kristofferkoch/oparroy/src/oparroy/dsl/ir.py

"""Core IR for the oparroy design-capture DSL (DESIGN.md §7).

The IR is a plain data structure — parts, pins, nets, one circuit —
built through the capture API (``Circuit.part`` / ``Circuit.net`` /
``Circuit.connect``: plain function calls in the HDL-instantiation
flavor, references are explicit instance names), validated by
``oparroy.dsl.check``, and consumed by the emitters. Structural
invariants (unique reference names, a pin on at most one net) raise at
construction; everything electrical is the validation pass's job.

Hierarchy is capture-time structure (§7): a circuit instantiates
subcircuits (``Circuit.instance``) with declared port interfaces
(``Circuit.port``), and ``Circuit.flatten`` is the pass that reduces
the hierarchy to the flat IR checks and emitters consume — instance
names prefix part references and internal nets, so identities stay
stable across source edits and findings report hierarchical paths.

Interfaces scale past scalar ports two ways (T7bb): port arrays
(``Circuit.port_array``) are width-fixed vectors bound element-wise,
and bundles (``Circuit.bundle``) group existing nets under member
names — the connector pinout as one connectable unit — bound
member-wise. Both expand to scalar port bindings at instantiation, so
flattening, checks, and emitters see plain nets only.

Multi-unit packages mirror KiCad's unit model (T7bc): ``Symbol``
preserves the unit structure, and a placed part instantiates a unit
subset — unplaced units materialize no pins, and a physical pin
shared by placed units is one ``Pin``, so KiCad ERC's shared-pin
one-net rule is structural in the IR. Component sockets
(``Circuit.socket``) let a subcircuit declare it needs a *part*, not
just nets: the instantiating parent directs the packing — a unit of a
parent-placed multi-unit package, or the socket protocol's standalone
default part — and the subcircuit stays package-agnostic.
"""

from __future__ import annotations

import re
from collections.abc import Iterable, Iterator, Mapping, Sequence
from dataclasses import dataclass
from enum import StrEnum
from typing import TYPE_CHECKING, ClassVar, Protocol, overload

if TYPE_CHECKING:
    from collections.abc import Callable

    from oparroy.dsl.parts import MultiUnitPart, TypedPart

type NetBinding = Net | str | Sequence[Net | str] | Mapping[str, Net | str]
type Connection = NetBinding | UnitHandle | type[TypedPart]

_NAT_SPLIT = re.compile(r"(\d+)")


def natural_key(text: str) -> tuple[tuple[str | int, ...], str]:
    """Sort key ordering embedded numbers numerically ("R2" < "R10").

    Keys equal after lowercasing and digit-splitting ("R1" vs "r1")
    fall back to the original string, so ordering never depends on
    insertion order.

    >>> natural_key("R10") > natural_key("R9")
    True
    """
    chunks = tuple(
        int(chunk) if chunk.isascii() and chunk.isdigit() else chunk
        for chunk in _NAT_SPLIT.split(text.lower())
    )
    return (chunks, text)


class PinType(StrEnum):
    """KiCad electrical pin types, valued as spelled in .kicad_sym files."""

    INPUT = "input"
    OUTPUT = "output"
    BIDIRECTIONAL = "bidirectional"
    TRI_STATE = "tri_state"
    PASSIVE = "passive"
    FREE = "free"
    UNSPECIFIED = "unspecified"
    POWER_IN = "power_in"
    POWER_OUT = "power_out"
    OPEN_COLLECTOR = "open_collector"
    OPEN_EMITTER = "open_emitter"
    NO_CONNECT = "no_connect"


class DefinitionError(Exception):
    """A structural IR invariant was violated during capture."""


def _reject_separator(kind: str, name: str) -> None:
    """Reject '/', the hierarchy path separator, in a captured name.

    Instance names, part references, and net names all become path
    elements under flattening (``WD1/Rs``, ``WD1/x``), so none may
    carry the separator — a '/' smuggled in at capture would collide
    with, or masquerade as, a flattened path.
    """
    if "/" in name:
        msg = f"{kind} {name!r} must not contain '/', the hierarchy path separator"
        raise DefinitionError(msg)


class UnknownSymbolError(DefinitionError):
    """A part referenced a symbol the symbol table does not know."""


_SOCKET_LIB = "socket"


def _pin_numbers(numbers: str | tuple[str, ...]) -> tuple[str, ...]:
    """Normalize a pin_map value to a tuple of pin numbers."""
    return (numbers,) if isinstance(numbers, str) else numbers


def _validate_socket_spec(spec: type[SocketSpec]) -> None:
    """Reject a malformed socket protocol at declaration."""
    # Lazy import: parts.py imports this module at runtime.
    from oparroy.dsl.parts import MultiUnitPart as _MultiUnitPart  # noqa: PLC0415
    from oparroy.dsl.parts import TypedPart as _TypedPart  # noqa: PLC0415

    if not (isinstance(spec, type) and issubclass(spec, SocketSpec)):
        msg = f"socket() needs a SocketSpec subclass, got {spec!r}"
        raise DefinitionError(msg)
    pins = getattr(spec, "pins", None)
    if (
        not isinstance(pins, tuple)
        or not pins
        or any(not isinstance(pin, str) or not pin for pin in pins)
        or len(set(pins)) != len(pins)
    ):
        msg = f"{spec.__name__}.pins must be a non-empty tuple of unique names"
        raise DefinitionError(msg)
    default = getattr(spec, "default", None)
    if not (isinstance(default, type) and issubclass(default, _TypedPart)):
        msg = f"{spec.__name__}.default must be a typed part class, got {default!r}"
        raise DefinitionError(msg)
    if issubclass(default, _MultiUnitPart):
        msg = (
            f"{spec.__name__}.default must be a standalone part, "
            f"not the multi-unit package {default.__name__}"
        )
        raise DefinitionError(msg)
    if set(default.pin_map) != set(pins):
        msg = (
            f"{spec.__name__}.default ({default.__name__}) has pins "
            f"{sorted(default.pin_map)}, not the protocol pins {sorted(pins)}"
        )
        raise DefinitionError(msg)


def _bind_part_class(
    name: str,
    ref: str,
    spec: type[SocketSpec],
    part_class: type[TypedPart],
) -> StandaloneSocket:
    """Validate a parent-directed standalone part class for a socket."""
    # Lazy import: parts.py imports this module at runtime.
    from oparroy.dsl.parts import MultiUnitPart as _MultiUnitPart  # noqa: PLC0415

    if issubclass(part_class, _MultiUnitPart):
        msg = (
            f"instance {name!r}: socket {ref!r} takes one unit of "
            f"{part_class.__name__} (u1.unit(3)), not the whole package"
        )
        raise DefinitionError(msg)
    if set(part_class.pin_map) != set(spec.pins):
        msg = (
            f"instance {name!r}: {part_class.__name__} does not satisfy "
            f"socket {ref!r}: pin names {sorted(part_class.pin_map)} != "
            f"protocol {sorted(spec.pins)}"
        )
        raise DefinitionError(msg)
    return StandaloneSocket(part_class=part_class)


@dataclass(frozen=True)
class Interval:
    """A closed interval [low, high] — one limit range.

    Containment is inclusive on both ends, so equal boundaries cover:

    >>> Interval(0, 3.6).contains(Interval(0, 3.3))
    True
    >>> Interval(0, 3.6).contains(Interval(0, 3.6))
    True
    >>> Interval(0, 3.3).contains(Interval(-0.3, 3.3))
    False
    """

    low: float
    high: float

    def __post_init__(self) -> None:
        if not self.low <= self.high:
            msg = f"interval low {self.low} exceeds high {self.high}"
            raise DefinitionError(msg)

    def contains(self, other: Interval) -> bool:
        """Return True when this interval fully covers ``other``."""
        return self.low <= other.low and other.high <= self.high

    def __str__(self) -> str:
        return f"{self.low}..{self.high}"


@dataclass(frozen=True)
class Limits:
    """A port's electrical limit ranges: voltage, optionally current.

    On a ``source`` port the ranges are what the driver puts out; on a
    ``sink`` port what the input accepts. The validation pass checks
    interval containment at instance bindings — the sink's range must
    cover the connected source's — so tolerance stackup is checkable
    data. ``current`` is optional: a port declaring voltage only checks
    voltage only.
    """

    voltage: Interval
    current: Interval | None = None

    def __str__(self) -> str:
        text = f"{self.voltage} V"
        if self.current is not None:
            text += f", {self.current} A"
        return text


@dataclass(frozen=True)
class Waiver:
    """An explicit, path-addressed check waiver: auditable data.

    Waivers live in the capture next to the wiring they excuse
    (``board.waive("range-containment", "WD1/ka", reason=...)``) — never
    comment-style suppression. ``path`` is the hierarchical path the
    finding reports. A waiver that matches no finding warns as stale.
    """

    check: str
    path: str
    reason: str


@dataclass(frozen=True)
class Provenance:
    """Base-design origin of a transform-created part or net.

    Instrumentation transforms (:mod:`oparroy.dsl.transform`) tag every
    part and net they create: ``transform`` is the transform record's
    label (``"F1"``), ``base`` the capture name of the base net it
    derives from, relative to the tile the transform applied in. The
    reset-state equivalence proof consumes exactly these tags —
    no name-matching heuristics. Base-capture elements carry None.
    """

    transform: str
    base: str


@dataclass(frozen=True, order=True)
class TileNet:
    """A net local to one tile instance, addressed for a pass's tables.

    The instance path plus the tile-local capture name —
    ``TileNet(("T0",), "sense")`` — identifies the net unambiguously
    across the board (it flattens to ``T0/sense``). The key shape of
    the transform ``Handles`` (:mod:`oparroy.dsl.transform`) and of the
    equivalence proof's reset-level and base-net tables: a named type
    because a bare ``tuple[tuple[str, ...], str]`` transposes its two
    components without a murmur (code-std-python.md#2-composite-types).

    >>> TileNet(("T0",), "sense").name
    'sense'
    """

    path: tuple[str, ...]
    name: str


@dataclass(frozen=True)
class Residuals:
    """Electrical residual magnitudes of a part in its pass-through state.

    The reset-state equivalence proof's magnitude source
    (``docs/instrumentation-equivalence.md`` §4 Q3): a closed analog
    switch is 7 Ω, not 0 Ω — the proof
    enumerates these per placed part against the residual register
    (``docs/instrumented-ci.md`` §9). Values come from the
    parts DB (``PartRecord.residuals``) via the typed part class; a
    field left None is no data, never zero. Geometry residuals (tap
    stub capacitance) are not expressible here — they are layout
    properties, emitted as layout-checker obligations.

    >>> r = Residuals(on_resistance_ohm=7.0, on_capacitance_pf=17.3)
    >>> r.on_resistance_ohm
    7.0
    """

    on_resistance_ohm: float | None = None
    on_capacitance_pf: float | None = None
    off_capacitance_pf: float | None = None
    leakage_ua: float | None = None

    def __post_init__(self) -> None:
        for field_name in (
            "on_resistance_ohm",
            "on_capacitance_pf",
            "off_capacitance_pf",
            "leakage_ua",
        ):
            value = getattr(self, field_name)
            if value is not None and value < 0:
                msg = f"residual {field_name} must not be negative, got {value}"
                raise DefinitionError(msg)


@dataclass(frozen=True)
class SymbolPin:
    """One pin of a library symbol: number, display name, electrical type."""

    number: str
    name: str
    type: PinType


@dataclass(frozen=True)
class SymbolUnit:
    """One placeable unit of a multi-unit symbol (DESIGN.md §7).

    KiCad encodes units as ``<Name>_<unit>_<style>`` subsymbols; each
    unit's pins carry physical package pin numbers, and one physical
    pin may appear in several units (the BAT54ADW shared anodes).
    """

    number: int
    pins: tuple[SymbolPin, ...]


@dataclass(frozen=True)
class Symbol:
    """A resolved library symbol: the pin-level contract of a part kind.

    ``pins`` is the all-units placement view; the unit structure
    (DESIGN.md §7) is ``common_pins`` — unit 0, present in every
    placed unit; the whole pin set of a single-unit symbol — and
    ``units``, the placeable units in unit-number order.
    """

    lib: str
    name: str
    pins: tuple[SymbolPin, ...]
    footprint_filters: tuple[str, ...] = ()
    pin_conflicts: tuple[str, ...] = ()
    common_pins: tuple[SymbolPin, ...] = ()
    units: tuple[SymbolUnit, ...] = ()

    @property
    def ref(self) -> str:
        """The canonical ``Lib:Name`` reference."""
        return f"{self.lib}:{self.name}"

    @property
    def is_power(self) -> bool:
        """True for power-library symbols (``power:+3V3``).

        Power symbols are schematic-only net markers: no footprint,
        excluded from the board netlist.
        """
        return self.lib == "power"

    @property
    def is_socket(self) -> bool:
        """True for component-socket placeholders (``Circuit.socket``).

        A socket placeholder carries the protocol pins a subcircuit
        wires against; flattening replaces it with the standalone part
        or the parent-placed package unit the parent directed.
        """
        return self.lib == _SOCKET_LIB

    def pin(self, number: str) -> SymbolPin | None:
        """Look up a pin by number, or None if the symbol has no such pin."""
        return next((p for p in self.pins if p.number == number), None)

    def pins_for_units(self, units: Iterable[int] | None) -> tuple[SymbolPin, ...]:
        """Return the pins a placement materializes for a unit subset.

        None places every unit (the default) — the whole ``pins``
        view. A subset places the common pins plus the chosen units'
        pins; unplaced units materialize no pins, so the
        unconnected-pin check stays clean. A physical pin shared by
        several placed units appears once.
        """
        if units is None:
            return self.pins
        known = {unit.number for unit in self.units}
        unknown = sorted(set(units) - known)
        if unknown:
            msg = f"{self.ref} has no units {unknown} (units: {sorted(known)})"
            raise DefinitionError(msg)
        wanted = set(units)
        merged: dict[str, SymbolPin] = {pin.number: pin for pin in self.common_pins}
        for unit in self.units:
            if unit.number in wanted:
                for pin in unit.pins:
                    merged[pin.number] = pin
        return tuple(merged.values())


class SymbolTable(Protocol):
    """Source of library symbols — kicadlib for real use, stubs in tests."""

    def lookup(self, ref: str) -> Symbol:
        """Resolve ``Lib:Name`` to a Symbol, raising UnknownSymbolError."""
        ...


class SocketSpec:
    """A component socket protocol: the pin handles a subcircuit needs.

    Subclasses (``oparroy.dsl.parts``) fix ``pins`` — the protocol pin
    names — and ``default``, the standalone typed part flattening
    places when the instantiating parent does not pack the socket into
    one unit of a parent-placed multi-unit package. Packing is the
    parent's directed choice; the subcircuit stays package-agnostic
    (DESIGN.md §7, T7bc).
    """

    pins: ClassVar[tuple[str, ...]]
    default: ClassVar[type[TypedPart]]


class Pin:
    """One pin of one placed part; carries its net membership."""

    def __init__(self, part: Part, symbol_pin: SymbolPin) -> None:
        self._part = part
        self._symbol_pin = symbol_pin
        self._net: Net | None = None

    @property
    def part(self) -> Part:
        """The part this pin belongs to."""
        return self._part

    @property
    def net(self) -> Net | None:
        """The net this pin sits on, or None; set only by circuit wiring."""
        return self._net

    @property
    def number(self) -> str:
        """The pin number as declared by the symbol ("1", "A3", ...)."""
        return self._symbol_pin.number

    @property
    def name(self) -> str:
        """The pin name as declared by the symbol ("" when unnamed)."""
        return self._symbol_pin.name

    @property
    def type(self) -> PinType:
        """The electrical type declared by the symbol."""
        return self._symbol_pin.type

    def __repr__(self) -> str:
        return f"<Pin {self._part.ref}.{self.number}>"


@dataclass(frozen=True)
class Placement:
    """How a placed part sits: hierarchy path and multi-unit selection.

    ``path`` is the instance path flattening stamps on the flat copy —
    the hierarchy metadata (sheetpath) the KiCad emitter and the
    layout checker key channelization on. ``units`` is the placed
    unit subset of a multi-unit symbol (None = every unit, today's
    behavior): only the placed units' pins materialize, and a
    physical pin shared by placed units is one ``Pin``.
    ``unit_names`` carries the typed per-unit pin names a
    ``MultiUnitPart`` placement declared — the currency of
    ``Part.unit`` handles. ``pin_names`` carries the typed pin
    keywords of a plain ``TypedPart`` placement (keyword → pin
    numbers), so passes can address pins by their capture names
    (``Rat.b``) — the instrumentation transforms' pin addressing.
    """

    path: tuple[str, ...] = ()
    units: tuple[int, ...] | None = None
    unit_names: dict[int, dict[str, str]] | None = None
    pin_names: dict[str, tuple[str, ...]] | None = None


class Part:
    """One placed component: an explicit reference bound to a symbol.

    ``provenance`` is None for base-capture parts; instrumentation
    transforms tag the parts they create. ``residuals`` carries the
    part's electrical residual magnitudes (:class:`Residuals`) when it
    was placed from a typed part whose class declares them (the parts
    DB's ``bind`` threads them through); None means no data.
    """

    def __init__(  # noqa: PLR0913 — ref/symbol/value/footprint + identity/placement
        self,
        ref: str,
        symbol: Symbol,
        value: str | None,
        footprint: str | None,
        *,
        identity: str | None = None,
        placement: Placement | None = None,
    ) -> None:
        self._ref = ref
        self._symbol = symbol
        self.value = value
        self.footprint = footprint
        self.provenance: Provenance | None = None
        self.residuals: Residuals | None = None
        self._identity = ref if identity is None else identity
        base = Placement() if placement is None else placement
        units = base.units
        if units is not None:
            if len(set(units)) != len(units):
                msg = f"{ref} places units {sorted(units)} with duplicates"
                raise DefinitionError(msg)
            base = Placement(
                path=base.path,
                units=tuple(sorted(units)),
                unit_names=base.unit_names,
                pin_names=base.pin_names,
            )
        self._placement = base
        self._pins = {sp.number: Pin(self, sp) for sp in symbol.pins_for_units(units)}

    @property
    def ref(self) -> str:
        """The reference designator, assigned explicitly at capture."""
        return self._ref

    @property
    def identity(self) -> str:
        """The capture name this part is known by, stable across stages.

        Equal to ``ref`` until annotation renames the part to its board
        refdes — the identity keeps the capture name (``WD1/Rs``) so the
        emitted tstamps survive re-annotation and pcbnew keeps matching
        the part by timestamp (DESIGN.md §7).
        """
        return self._identity

    @property
    def path(self) -> tuple[str, ...]:
        """The instance path this part was flattened through.

        Empty for a directly placed part; set by ``Circuit.flatten`` on
        the flat copy — the hierarchy metadata (sheetpath) the KiCad
        emitter and the layout checker key channelization on.
        """
        return self._placement.path

    @property
    def symbol(self) -> Symbol:
        """The library symbol this part instantiates."""
        return self._symbol

    @property
    def units(self) -> tuple[int, ...] | None:
        """The placed unit subset, or None when every unit is placed."""
        return self._placement.units

    @property
    def pin_names(self) -> dict[str, tuple[str, ...]] | None:
        """The typed pin keywords this part was placed with, keyword → numbers.

        Set for parts placed from a plain ``TypedPart`` (a keyword may
        own several pin numbers, like a connector's ground member);
        None for symbol-placed and multi-unit parts. Transform pin
        addresses (``Rat.b``) resolve through it.
        """
        return self._placement.pin_names

    @property
    def pins(self) -> tuple[Pin, ...]:
        """All pins, ordered by pin number."""
        return tuple(self._pins[n] for n in sorted(self._pins, key=natural_key))

    def pin(self, number: int | str) -> Pin:
        """Look up a pin by number; raises DefinitionError if absent."""
        key = str(number)
        try:
            return self._pins[key]
        except KeyError:
            msg = f"{self._ref} ({self._symbol.ref}) has no pin {key}"
            raise DefinitionError(msg) from None

    def unit(self, number: int) -> UnitHandle:
        """Return a typed handle over one placed unit's pins.

        Available on parts placed from a multi-unit typed part
        (``oparroy.dsl.parts.MultiUnitPart``), which declares the pin
        names; wire the unit (``connect(net, u1.unit(1).anode)``) or
        hand the handle to a subcircuit's component socket.
        """
        unit_names = self._placement.unit_names
        if unit_names is None:
            msg = (
                f"{self._ref} ({self._symbol.ref}) was not placed from a "
                "multi-unit typed part; wire its pins by number"
            )
            raise DefinitionError(msg)
        try:
            names = unit_names[number]
        except KeyError:
            placed = sorted(unit_names)
            msg = f"{self._ref} has no placed unit {number} (placed: {placed})"
            raise DefinitionError(msg) from None
        return UnitHandle(self, number, names)

    def _flattened_placement(self, path: tuple[str, ...]) -> Placement:
        """Return the placement for the flat copy: same units, path prefixed.

        The part's existing path elements survive under the new prefix:
        a part already flattened per-tile by the instrumentation
        transform pass (``Instance.flatten_hierarchy``) carries its
        in-tile path (``("PHY1",)``), and the parent's flatten prepends
        the instance path (``("T0", "PHY1")``). Captured parts have an
        empty path, so plain flattening is unchanged.
        """
        names = self._placement.unit_names
        pin_names = self._placement.pin_names
        return Placement(
            path=(*path, *self._placement.path),
            units=self._placement.units,
            unit_names=None
            if names is None
            else {u: dict(pins) for u, pins in names.items()},
            pin_names=None if pin_names is None else dict(pin_names),
        )

    def __getitem__(self, number: int | str) -> Pin:
        return self.pin(number)

    def __repr__(self) -> str:
        return f"<Part {self._ref} {self._symbol.ref}>"


class UnitHandle(Mapping[str, Pin]):
    """One placed unit of a multi-unit part, by typed pin names.

    The packing currency (DESIGN.md §7): wire a unit at board level
    (``board.connect(net, u1.unit(1).anode)``), or hand it to a
    subcircuit's component socket at instantiation — packing is the
    parent's directed choice. Pins read by item (``handle["anode"]``)
    or attribute (``handle.anode``).
    """

    def __init__(self, part: Part, unit: int, pin_names: dict[str, str]) -> None:
        self._part = part
        self._unit = unit
        self._pin_names = dict(pin_names)

    @property
    def part(self) -> Part:
        """The placed package part this unit belongs to."""
        return self._part

    @property
    def unit(self) -> int:
        """The unit number within the package."""
        return self._unit

    @property
    def pin_map(self) -> dict[str, str]:
        """Pin keyword name → physical pin number."""
        return dict(self._pin_names)

    def __getitem__(self, name: str) -> Pin:
        try:
            number = self._pin_names[name]
        except KeyError:
            raise KeyError(
                f"{self._part.ref} unit {self._unit} has no pin {name!r}"
            ) from None
        return self._part.pin(number)

    def __iter__(self) -> Iterator[str]:
        return iter(self._pin_names)

    def __len__(self) -> int:
        return len(self._pin_names)

    def __getattr__(self, name: str) -> Pin:
        try:
            number = self.__dict__["_pin_names"][name]
        except KeyError:
            raise AttributeError(
                f"{self.__dict__['_part'].ref} unit {self.__dict__['_unit']} "
                f"has no pin {name!r}"
            ) from None
        return self.__dict__["_part"].pin(number)

    def __repr__(self) -> str:
        return f"<UnitHandle {self._part.ref} unit {self._unit}>"


class Net:
    """A named equipotential: the set of pins joined together.

    ``provenance`` is None for base-capture nets; instrumentation
    transforms tag the nets they create.
    """

    def __init__(
        self,
        name: str,
        *,
        is_port: bool = False,
        source: Limits | None = None,
        sink: Limits | None = None,
    ) -> None:
        self._name = name
        self._is_port = is_port
        self._source = source
        self._sink = sink
        self._pins: list[Pin] = []
        self.provenance: Provenance | None = None

    @property
    def name(self) -> str:
        """The net name as it appears in emitted netlists."""
        return self._name

    @property
    def is_port(self) -> bool:
        """True for ports — external-facing nets (``Circuit.port``).

        A port is the subcircuit interface: ``Circuit.instance`` binds
        every port to a parent net, and flattening merges the two.
        """
        return self._is_port

    @property
    def source(self) -> Limits | None:
        """The limit ranges this port drives, or None when undeclared."""
        return self._source

    @property
    def sink(self) -> Limits | None:
        """The limit ranges this port accepts, or None when undeclared."""
        return self._sink

    @property
    def pins(self) -> tuple[Pin, ...]:
        """Member pins, ordered by part reference then pin number."""
        return tuple(
            sorted(
                self._pins,
                key=lambda p: (natural_key(p.part.ref), natural_key(p.number)),
            )
        )

    def _attach(self, pin: Pin) -> None:
        """Add a pin to this net; called by ``Circuit.connect``.

        Re-attaching to the net the pin already sits on is a no-op: a
        physical pin shared by several placed units (DESIGN.md §7 —
        the BAT54ADW anodes) is legitimately wired once per unit, and
        KiCad ERC's shared-pin rule allows exactly the one net.
        """
        if pin.net is self:
            return
        if pin.net is not None:
            msg = f"{pin.part.ref}.{pin.number} is already on net {pin.net.name!r}"
            raise DefinitionError(msg)
        pin._net = self  # noqa: SLF001 — same module; Pin.net is module-private
        self._pins.append(pin)

    def _detach(self, pin: Pin) -> None:
        """Remove a pin from this net; called by ``Circuit.cut_net``."""
        self._pins.remove(pin)
        pin._net = None  # noqa: SLF001 — same module; Pin.net is module-private

    def __repr__(self) -> str:
        return f"<Net {self._name} ({len(self._pins)} pins)>"


class PortArray(Sequence[Net]):
    """A port vector of ``width`` port nets (``name[0]``, ``name[1]``, …).

    The array interface — button matrices, LED arrays (T7bb). Captures
    index it like any sequence; ``Circuit.instance`` binds it to a
    sequence of parent nets of equal width and flattening merges
    element-wise, so a width drift raises at capture.
    """

    def __init__(self, name: str, nets: tuple[Net, ...]) -> None:
        self._name = name
        self._nets = nets

    @property
    def name(self) -> str:
        """The array base name; the element nets are ``name[i]``."""
        return self._name

    @property
    def nets(self) -> tuple[Net, ...]:
        """The element nets, in index order."""
        return self._nets

    def __len__(self) -> int:
        return len(self._nets)

    @overload
    def __getitem__(self, index: int) -> Net: ...
    @overload
    def __getitem__(self, index: slice) -> tuple[Net, ...]: ...
    def __getitem__(self, index: int | slice) -> Net | tuple[Net, ...]:
        return self._nets[index]

    def __repr__(self) -> str:
        return f"<PortArray {self._name}[{len(self)}]>"


class Bundle(Mapping[str, Net]):
    """A named group of nets, connectable as one unit (T7bb).

    Members alias existing nets under bundle-local names — the §3
    segment pinout: ``upstream.a`` is a node's RX_A port,
    ``downstream.a`` its TX_A, and the two faces join member-to-member.
    ``Circuit.instance`` binds a bundle port to a same-membered bundle
    or mapping; ``BundleConnector`` maps members to connector pin
    numbers declaratively. Member access works by item
    (``bundle["a"]``) or attribute (``bundle.a``); a member shadowing a
    class attribute (``name``, …) stays reachable by item.
    """

    def __init__(self, name: str, members: dict[str, Net]) -> None:
        self._name = name
        self._members = dict(members)

    @property
    def name(self) -> str:
        """The bundle name — the binding keyword at instantiation."""
        return self._name

    def __getitem__(self, member: str) -> Net:
        try:
            return self._members[member]
        except KeyError:
            raise KeyError(f"bundle {self._name!r} has no member {member!r}") from None

    def __iter__(self) -> Iterator[str]:
        return iter(self._members)

    def __len__(self) -> int:
        return len(self._members)

    def __getattr__(self, member: str) -> Net:
        try:
            return self.__dict__["_members"][member]
        except KeyError:
            raise AttributeError(
                f"bundle {self._name!r} has no member {member!r}"
            ) from None

    def __repr__(self) -> str:
        return f"<Bundle {self._name}: {' '.join(self._members)}>"


def _expand_connections(
    instance_name: str,
    child: Circuit,
    connections: dict[str, NetBinding],
) -> dict[str, list[tuple[Net | str, str]]]:
    """Expand array/bundle bindings into per-port connections.

    Every expanded entry carries its source label for conflict reports;
    a port reached twice (the §3 power nets, aliased into both
    segment-face bundles) keeps both entries, and ``Circuit.instance``
    resolves them to one parent net.
    """
    expanded: dict[str, list[tuple[Net | str, str]]] = {}
    for key, value in connections.items():
        if key in child._arrays:  # noqa: SLF001 — same module
            entries = _expand_array(instance_name, child._arrays[key], value)  # noqa: SLF001
        elif key in child._bundles:  # noqa: SLF001 — same module
            entries = _expand_bundle(instance_name, child._bundles[key], value)  # noqa: SLF001
        elif isinstance(value, Net | str):
            entries = {key: (value, key)}
        else:
            msg = (
                f"instance {instance_name!r}: port {key!r} bound to {value!r}, "
                "not a net"
            )
            raise DefinitionError(msg)
        for port_name, entry in entries.items():
            expanded.setdefault(port_name, []).append(entry)
    return expanded


def _expand_array(
    instance_name: str,
    array: PortArray,
    value: Net | str | Sequence[Net | str] | Mapping[str, Net | str],
) -> dict[str, tuple[Net | str, str]]:
    """Expand an array binding into per-element ``name[i]`` connections."""
    width = len(array)
    if isinstance(value, str) or not isinstance(value, Sequence):
        msg = (
            f"instance {instance_name!r}: port {array.name!r} is an array of "
            f"width {width}; bind a sequence of {width} nets"
        )
        raise DefinitionError(msg)
    elements = list(value)
    if len(elements) != width:
        msg = (
            f"instance {instance_name!r}: port array {array.name!r} has "
            f"width {width}, bound to {len(elements)} nets"
        )
        raise DefinitionError(msg)
    expanded: dict[str, tuple[Net | str, str]] = {}
    for index, element in enumerate(elements):
        if not isinstance(element, Net | str):
            msg = (
                f"instance {instance_name!r}: port array {array.name!r} "
                f"element {index} bound to {element!r}, not a net"
            )
            raise DefinitionError(msg)
        # The source label is the array binding keyword, not the
        # element name — a conflict with an individual element binding
        # must name two distinguishable sources.
        expanded[f"{array.name}[{index}]"] = (element, array.name)
    return expanded


def _expand_bundle(
    instance_name: str,
    bundle: Bundle,
    value: Net | str | Sequence[Net | str] | Mapping[str, Net | str],
) -> dict[str, tuple[Net | str, str]]:
    """Expand a bundle binding into per-member port connections."""
    members = list(bundle)
    if not isinstance(value, Mapping):
        msg = (
            f"instance {instance_name!r}: port {bundle.name!r} is a bundle "
            f"with members {members}; bind a bundle or a mapping"
        )
        raise DefinitionError(msg)
    supplied = dict(value)
    unknown = sorted(set(supplied) - set(members), key=natural_key)
    missing = sorted(set(members) - set(supplied), key=natural_key)
    if unknown or missing:
        problems = []
        if missing:
            problems.append(f"missing {missing}")
        if unknown:
            problems.append(f"unknown {unknown}")
        msg = (
            f"instance {instance_name!r}: bundle {bundle.name!r} binding has "
            f"{' and '.join(problems)} (members: {members})"
        )
        raise DefinitionError(msg)
    expanded = {}
    for member in members:
        net = supplied[member]
        if not isinstance(net, Net | str):
            msg = (
                f"instance {instance_name!r}: bundle {bundle.name!r} member "
                f"{member!r} bound to {net!r}, not a net"
            )
            raise DefinitionError(msg)
        expanded[bundle[member].name] = (net, f"{bundle.name}.{member}")
    return expanded


@dataclass(frozen=True)
class PackedSocket:
    """A socket satisfied by one unit of a parent-placed package."""

    part: Part
    unit: int
    pin_map: dict[str, str]


@dataclass(frozen=True)
class StandaloneSocket:
    """A socket satisfied by a parent-directed standalone typed part class."""

    part_class: type[TypedPart]


class Instance:
    """One placed subcircuit: a captured child with its ports bound.

    Built by ``Circuit.instance``; carries the child circuit, the port
    bindings (port name → parent net), and the socket bindings
    (socket reference → packing decision) that ``Circuit.flatten``
    consumes. The capture callable is kept as the instance's subcircuit
    identity — the sheetpath key the instrumentation transform pass
    (:mod:`oparroy.dsl.transform`) scopes per-tile declarations on.
    """

    def __init__(
        self,
        name: str,
        circuit: Circuit,
        connections: dict[str, Net],
        socket_bindings: dict[str, PackedSocket | StandaloneSocket],
        *,
        subcircuit: Callable[[Circuit], None] | None = None,
    ) -> None:
        self._name = name
        self._circuit = circuit
        self._connections = dict(connections)
        self._socket_bindings = dict(socket_bindings)
        self._subcircuit = subcircuit

    @property
    def name(self) -> str:
        """The instance name — the hierarchy path element."""
        return self._name

    @property
    def circuit(self) -> Circuit:
        """The captured child circuit."""
        return self._circuit

    @property
    def subcircuit(self) -> Callable[[Circuit], None] | None:
        """The capture callable this instance was built from.

        A ``Subcircuit`` instance (match on its type for per-tile
        keying) or any capture callable (match on identity); None only
        for a hand-built Instance.
        """
        return self._subcircuit

    @property
    def connections(self) -> dict[str, Net]:
        """Port bindings: port name → the parent net it sits on."""
        return dict(self._connections)

    @property
    def socket_bindings(self) -> dict[str, PackedSocket | StandaloneSocket]:
        """Socket bindings: socket reference → the packing decision."""
        return dict(self._socket_bindings)

    def bind(self, port: str, net: Net) -> None:
        """Bind a port after instantiation: late binding for pass machinery.

        Instrumentation transforms add control and tap ports to
        an already-placed instance's child; this binds one to its
        parent net. ``port`` must name an unbound port of the child
        circuit; the net's membership in the parent is the caller's
        responsibility (the transform engine validates it).
        """
        target = self._circuit._nets.get(port)  # noqa: SLF001 — same module
        if target is None or not target.is_port:
            msg = f"instance {self._name!r}: the child has no port {port!r}"
            raise DefinitionError(msg)
        if port in self._connections:
            msg = f"instance {self._name!r}: port {port!r} is already bound"
            raise DefinitionError(msg)
        self._connections[port] = net

    def flatten_hierarchy(self) -> Circuit:
        """Flatten the captured child's own hierarchy in place.

        Pass machinery (the instrumentation transforms) operates on
        the per-tile flat form: the child's internal instances resolve
        (``PHY1/Rat`` refs, in-tile paths), ports keep their names and
        flags, waivers are preserved with their paths prefixed, and
        socket bindings are consumed. Semantically transparent to the
        parent's flatten — refs, nets, and paths come out as if the
        child had never been touched. Idempotent.
        """
        for binding in self._socket_bindings.values():
            if isinstance(binding, PackedSocket):
                msg = (
                    f"instance {self._name!r}: cannot flatten a child whose "
                    "sockets are packed into parent-placed units — the "
                    "parent parts are out of reach"
                )
                raise DefinitionError(msg)
        flat = Circuit(
            self._circuit._name,  # noqa: SLF001 — same module
            self._circuit._symbols,  # noqa: SLF001 — same module
        )
        self._circuit._flatten_into(flat, (), {}, self._socket_bindings)  # noqa: SLF001
        flat._waivers.extend(hierarchical_waivers(self._circuit))  # noqa: SLF001
        self._circuit = flat
        self._socket_bindings = {}
        return flat

    def __repr__(self) -> str:
        return f"<Instance {self._name} of {self._circuit.name!r}>"


class Circuit:
    """One captured circuit: parts and nets, the unit of check and emit."""

    def __init__(self, name: str, symbols: SymbolTable) -> None:
        if not name:
            msg = "circuit name must not be empty"
            raise DefinitionError(msg)
        self._name = name
        self._symbols = symbols
        self._parts: dict[str, Part] = {}
        self._nets: dict[str, Net] = {}
        self._arrays: dict[str, PortArray] = {}
        self._bundles: dict[str, Bundle] = {}
        self._instances: dict[str, Instance] = {}
        self._waivers: list[Waiver] = []
        self._sockets: dict[str, type[SocketSpec]] = {}
        self._allocations: dict[tuple[str, int], str] = {}

    @property
    def name(self) -> str:
        """The circuit name, used in emitted design headers."""
        return self._name

    @property
    def parts(self) -> dict[str, Part]:
        """All parts by reference (insertion order)."""
        return dict(self._parts)

    @property
    def nets(self) -> dict[str, Net]:
        """All nets by name (insertion order)."""
        return dict(self._nets)

    @property
    def ports(self) -> dict[str, Net]:
        """Port nets by name — the subcircuit interface (insertion order)."""
        return {name: net for name, net in self._nets.items() if net.is_port}

    @property
    def port_arrays(self) -> dict[str, PortArray]:
        """Port arrays by name — the vector interface (insertion order)."""
        return dict(self._arrays)

    @property
    def bundles(self) -> dict[str, Bundle]:
        """Bundles by name — the grouped interface (insertion order)."""
        return dict(self._bundles)

    @property
    def instances(self) -> dict[str, Instance]:
        """All subcircuit instances by name (insertion order)."""
        return dict(self._instances)

    @property
    def waivers(self) -> tuple[Waiver, ...]:
        """The capture's check waivers, in declaration order."""
        return tuple(self._waivers)

    def waive(self, check: str, path: str, *, reason: str) -> Waiver:
        """Waive one check finding by hierarchical path, with a reason.

        Waivers are explicit, path-addressed data in the capture —
        auditable in review, never comment-style suppression.
        ``check`` is the check id the finding carries (e.g.
        ``"range-containment"``); ``path`` is the '/'-separated
        hierarchical path it reports (``WD1/ka``), relative to this
        circuit — declared inside a subcircuit, instantiation prefixes
        it (``IN1/vin`` inside ``WD1`` addresses ``WD1/IN1/vin``). A
        waived error degrades to a WAIVED finding — visible, not erased
        — and a waiver that matches no finding warns as stale.
        """
        if not check:
            msg = "a waiver needs a check id"
            raise DefinitionError(msg)
        if not path:
            msg = f"a waiver for {check!r} needs a path"
            raise DefinitionError(msg)
        if not reason:
            msg = f"a waiver for {check!r} at {path!r} needs a reason"
            raise DefinitionError(msg)
        if any(w.check == check and w.path == path for w in self._waivers):
            msg = f"duplicate waiver for {check!r} at {path!r}"
            raise DefinitionError(msg)
        waiver = Waiver(check, path, reason)
        self._waivers.append(waiver)
        return waiver

    @property
    def sockets(self) -> dict[str, type[SocketSpec]]:
        """Component sockets by reference — the part interface (insertion order)."""
        return dict(self._sockets)

    def part(
        self,
        ref: str,
        spec: TypedPart | None = None,
        *,
        symbol: str | None = None,
        value: str | None = None,
        footprint: str | None = None,
    ) -> Part:
        """Place a part, from a typed spec or a ``Lib:Name`` symbol.

        A typed ``spec`` (``oparroy.dsl.parts``) carries its own
        symbol, value, footprint default, and wiring: placement
        connects its pins in the same step, and every net is resolved
        before anything is placed, so a rejected call changes nothing.
        A ``symbol`` string places an unwired part; wiring is
        ``connect``'s job. ``footprint`` overrides the spec's default.
        A multi-unit package's placed unit subset is declared by its
        typed part class (``oparroy.dsl.parts.MultiUnitPart``).
        """
        _reject_separator("part reference", ref)
        if isinstance(spec, str):
            msg = f"symbol {spec!r} must be passed as symbol={spec!r}"
            raise DefinitionError(msg)
        if spec is not None:
            if symbol is not None:
                msg = "pass a typed part or symbol=, not both"
                raise DefinitionError(msg)
            if value is not None:
                msg = "value goes to the typed part class, not part()"
                raise DefinitionError(msg)
            return self._place_typed(ref, spec, footprint)
        if symbol is None:
            msg = "part() needs a typed part or symbol="
            raise DefinitionError(msg)
        return self._place(ref, self._symbols.lookup(symbol), value, footprint)

    def _place_typed(
        self,
        ref: str,
        spec: TypedPart,
        footprint: str | None,
    ) -> Part:
        # Lazy import: parts.py imports this module at runtime.
        from oparroy.dsl.parts import MultiUnitPart as _MultiUnitPart  # noqa: PLC0415
        from oparroy.dsl.parts import TypedPart as _TypedPart  # noqa: PLC0415

        if not isinstance(spec, _TypedPart):
            msg = f"expected a typed part (oparroy.dsl.parts), got {spec!r}"
            raise DefinitionError(msg)
        resolved = self._symbols.lookup(spec.symbol)
        if isinstance(spec, _MultiUnitPart):
            placed = self._place_multi(ref, spec, footprint, resolved)
            placed.residuals = spec.residuals
            return placed
        symbol_pins = {pin.number for pin in resolved.pins}
        targets = [
            number
            for mapped in spec.pin_map.values()
            for number in _pin_numbers(mapped)
        ]
        unknown = sorted(set(targets) - symbol_pins, key=natural_key)
        if unknown:
            msg = (
                f"{type(spec).__name__} pin_map targets pins {unknown}, "
                f"which {spec.symbol} does not have"
            )
            raise DefinitionError(msg)
        if len(set(targets)) != len(targets):
            msg = (
                f"{type(spec).__name__} pin_map maps several names "
                "to the same pin number"
            )
            raise DefinitionError(msg)
        wiring = {kw: self._resolve_net(net) for kw, net in spec.nets.items()}
        placed = self._place(
            ref,
            resolved,
            spec.value,
            footprint if footprint is not None else spec.footprint,
            placement=Placement(
                pin_names={
                    kw: _pin_numbers(mapped) for kw, mapped in spec.pin_map.items()
                }
            ),
        )
        for kw, net in wiring.items():
            for number in _pin_numbers(spec.pin_map[kw]):
                net._attach(placed.pin(number))  # noqa: SLF001 — same module
        placed.residuals = spec.residuals
        return placed

    def _place_multi(
        self,
        ref: str,
        spec: MultiUnitPart,
        footprint: str | None,
        resolved: Symbol,
    ) -> Part:
        """Place a multi-unit typed part: validate the declared units.

        The declared ``unit_pins`` are the placed unit subset (DESIGN
        §7): each declared unit must exist in the symbol and map its
        pin names onto pins of that unit (or the common unit). One
        physical pin number repeating *across* units is the shared-pin
        case and stays legal; within one unit it is a pin swap.
        """
        by_unit = {u.number: {p.number for p in u.pins} for u in resolved.units}
        common = {p.number for p in resolved.common_pins}
        unknown_units = sorted(set(spec.unit_pins) - set(by_unit))
        if unknown_units:
            msg = (
                f"{type(spec).__name__} declares units {unknown_units}, "
                f"which {spec.symbol} does not have"
            )
            raise DefinitionError(msg)
        for unit, pin_map in sorted(spec.unit_pins.items()):
            unknown = sorted(
                set(pin_map.values()) - by_unit[unit] - common, key=natural_key
            )
            if unknown:
                msg = (
                    f"{type(spec).__name__} unit {unit} maps pins {unknown}, "
                    f"which {spec.symbol} unit {unit} does not have"
                )
                raise DefinitionError(msg)
            if len(set(pin_map.values())) != len(pin_map):
                msg = (
                    f"{type(spec).__name__} unit {unit} maps several names "
                    "to the same pin number"
                )
                raise DefinitionError(msg)
        return self._place(
            ref,
            resolved,
            spec.value,
            footprint if footprint is not None else spec.footprint,
            placement=Placement(
                units=tuple(sorted(spec.unit_pins)),
                unit_names={unit: dict(pins) for unit, pins in spec.unit_pins.items()},
            ),
        )

    def _place(  # noqa: PLR0913 — ref/symbol/value/footprint + identity/placement
        self,
        ref: str,
        resolved: Symbol,
        value: str | None,
        footprint: str | None,
        *,
        identity: str | None = None,
        placement: Placement | None = None,
    ) -> Part:
        if ref in self._parts:
            msg = f"duplicate part reference {ref!r}"
            raise DefinitionError(msg)
        placed = Part(
            ref, resolved, value, footprint, identity=identity, placement=placement
        )
        self._parts[ref] = placed
        return placed

    def net(self, name: str) -> Net:
        """Declare a net by name; duplicate names are an error."""
        _reject_separator("net name", name)
        return self._add_net(name, is_port=False)

    def port(
        self,
        name: str,
        *,
        source: Limits | None = None,
        sink: Limits | None = None,
    ) -> Net:
        """Declare a port: an external-facing net, the subcircuit interface.

        A port wires like any net inside the subcircuit; a parent
        instantiating it binds every port (``Circuit.instance``), and
        flattening merges port and bound net. Port nets are exempt from
        the dangling-net checks — reaching outside is their job.

        ``source``/``sink`` carry the port's electrical limit ranges:
        what this port drives out, what it accepts in. The
        validation pass checks interval containment wherever an
        instance binds a declared port to a declared parent net. A
        pass-through port may declare both faces — what it accepts from
        its parent and what it passes on to its children.
        """
        _reject_separator("net name", name)
        return self._add_net(name, is_port=True, source=source, sink=sink)

    def socket(self, ref: str, spec: type[SocketSpec]) -> Part:
        """Declare a component socket: this circuit needs a *part*, not nets.

        The socket's protocol pins (``spec.pins``) are pin handles the
        capture wires like any part's pins — ``connect(net, d["anode"])``
        — but no real part is placed yet: the instantiating parent
        directs the packing (``Circuit.instance``), either handing the
        socket one unit of a parent-placed multi-unit package or a
        standalone typed part class, and an unbound socket materializes
        as the protocol's ``default`` part at flattening. The
        subcircuit stays package-agnostic (DESIGN.md §7, T7bc).
        """
        _reject_separator("socket reference", ref)
        if ref in self._sockets:
            msg = f"duplicate socket reference {ref!r}"
            raise DefinitionError(msg)
        if ref in self._nets:
            msg = f"socket reference {ref!r} collides with a net of the same name"
            raise DefinitionError(msg)
        _validate_socket_spec(spec)
        symbol = Symbol(
            lib=_SOCKET_LIB,
            name=spec.__name__,
            pins=tuple(
                SymbolPin(number=name, name=name, type=PinType.PASSIVE)
                for name in spec.pins
            ),
        )
        placed = self._place(ref, symbol, None, None)
        self._sockets[ref] = spec
        return placed

    def port_array(self, name: str, width: int) -> PortArray:
        """Declare a port array: ``width`` port nets ``name[0]`` … ``name[width-1]``.

        The vector interface (button matrices, LED arrays). Width is
        fixed at declaration — the parent binds exactly ``width`` nets
        (``Circuit.instance``) and flattening merges element-wise, so a
        width drift raises at capture. Element nets also bind
        individually by name (``led[0]``=…) when a parent wires them
        one by one.
        """
        _reject_separator("port array name", name)
        if "[" in name or "]" in name:
            msg = f"port array name {name!r} must not contain '[' or ']'"
            raise DefinitionError(msg)
        if width < 1:
            msg = f"port array {name!r} needs a width of at least 1"
            raise DefinitionError(msg)
        self._check_group_name_free("port array", name)
        element_names = [f"{name}[{i}]" for i in range(width)]
        collisions = [n for n in element_names if n in self._nets]
        if collisions:
            msg = f"port array {name!r} collides with existing nets {collisions}"
            raise DefinitionError(msg)
        array = PortArray(
            name,
            tuple(self._add_net(n, is_port=True) for n in element_names),
        )
        self._arrays[name] = array
        return array

    def bundle(self, name: str, /, **members: Net | str) -> Bundle:
        """Group existing nets under member names, connectable as one unit.

        Members alias nets of this circuit — ports for a subcircuit
        interface (the §3 segment pinout), plain nets for a board-level
        link. ``Circuit.instance`` binds a bundle to a same-membered
        ``Bundle`` or a mapping; ``parts.BundleConnector`` maps members
        to connector pin numbers declaratively. One net may not alias
        two members of the same bundle (a member would bind nothing —
        multi-pin members are the connector block's tuple pin_map).
        """
        _reject_separator("bundle name", name)
        self._check_group_name_free("bundle", name)
        if not members:
            msg = f"bundle {name!r} needs at least one member"
            raise DefinitionError(msg)
        resolved: dict[str, Net] = {}
        for member, net in members.items():
            if not member:
                msg = f"bundle {name!r} has an empty member name"
                raise DefinitionError(msg)
            _reject_separator(f"bundle {name!r} member", member)
            resolved[member] = self._resolve_net(net)
        aliased: dict[Net, str] = {}
        for member, net in resolved.items():
            if net in aliased:
                msg = (
                    f"bundle {name!r}: members {aliased[net]!r} and "
                    f"{member!r} alias the same net {net.name!r}"
                )
                raise DefinitionError(msg)
            aliased[net] = member
        created = Bundle(name, resolved)
        self._bundles[name] = created
        return created

    def _check_group_name_free(self, kind: str, name: str) -> None:
        if name in self._arrays or name in self._bundles:
            msg = f"duplicate {kind} name {name!r}"
            raise DefinitionError(msg)
        if name in self._nets:
            msg = f"{kind} name {name!r} collides with a net of the same name"
            raise DefinitionError(msg)

    def _add_net(
        self,
        name: str,
        *,
        is_port: bool,
        source: Limits | None = None,
        sink: Limits | None = None,
    ) -> Net:
        if name in self._nets:
            msg = f"duplicate net name {name!r}"
            raise DefinitionError(msg)
        if name in self._arrays or name in self._bundles:
            msg = f"net name {name!r} collides with a port array or bundle"
            raise DefinitionError(msg)
        if name in self._sockets:
            msg = f"net name {name!r} collides with a socket of the same name"
            raise DefinitionError(msg)
        created = Net(name, is_port=is_port, source=source, sink=sink)
        self._nets[name] = created
        return created

    def connect(self, net: Net | str, *pins: Pin) -> None:
        """Join pins onto a net; a pin may sit on exactly one net.

        Reconnecting a pin to the net it already sits on is a no-op —
        the shared physical pin of a multi-unit package is wired once
        per unit (DESIGN.md §7). Validates every pin (circuit
        membership, not already connected elsewhere) before attaching
        any, so a rejected call changes nothing.
        """
        resolved = self._resolve_net(net)
        seen: set[Pin] = set()
        for pin in pins:
            if pin.part is not self._parts.get(pin.part.ref):
                msg = (
                    f"{pin.part.ref}.{pin.number} does not belong "
                    f"to circuit {self._name!r}"
                )
                raise DefinitionError(msg)
            if pin in seen:
                msg = f"{pin.part.ref}.{pin.number} listed twice in connect"
                raise DefinitionError(msg)
            seen.add(pin)
            if pin.net is not None and pin.net is not resolved:
                msg = f"{pin.part.ref}.{pin.number} is already on net {pin.net.name!r}"
                raise DefinitionError(msg)
        for pin in pins:
            resolved._attach(pin)  # noqa: SLF001 — same module

    def _resolve_net(self, net: Net | str) -> Net:
        if isinstance(net, Net):
            if self._nets.get(net.name) is not net:
                msg = f"net {net.name!r} does not belong to circuit {self._name!r}"
                raise DefinitionError(msg)
            return net
        try:
            return self._nets[net]
        except KeyError:
            msg = f"no net named {net!r} in circuit {self._name!r}"
            raise DefinitionError(msg) from None

    def cut_net(self, net: Net | str, pins: Iterable[Pin], *, name: str) -> Net:
        """Move pins off a net onto a fresh net: the split primitive.

        Pass machinery (the instrumentation transforms) cuts a net
        into sides by moving each side's pins out; every pin must sit
        on ``net``. Moving every pin out is legal — the emptied net is
        ``remove_net``'s to delete. The new net is internal (never a
        port): the interface side stays on the original net, which
        keeps its name, port flag, and limit ranges.
        """
        resolved = self._resolve_net(net)
        moved = list(pins)
        if not moved:
            msg = f"cut_net on {resolved.name!r} needs at least one pin"
            raise DefinitionError(msg)
        if len(set(moved)) != len(moved):
            msg = f"cut_net on {resolved.name!r} lists a pin twice"
            raise DefinitionError(msg)
        for pin in moved:
            if pin.net is not resolved:
                msg = f"{pin.part.ref}.{pin.number} is not on net {resolved.name!r}"
                raise DefinitionError(msg)
        created = self._add_net(name, is_port=False)
        for pin in moved:
            resolved._detach(pin)  # noqa: SLF001 — same module
            created._attach(pin)  # noqa: SLF001 — same module
        return created

    def remove_net(self, name: str) -> None:
        """Delete a pin-less internal net — the empty remnant of a cut."""
        resolved = self._resolve_net(name)
        if resolved.pins:
            msg = f"net {name!r} still has pins"
            raise DefinitionError(msg)
        if resolved.is_port:
            msg = f"net {name!r} is a port — ports are the interface contract"
            raise DefinitionError(msg)
        del self._nets[name]

    def export_net(self, name: str) -> Net:
        """Promote an internal net to the interface: a port in place.

        Pass machinery (the ``AddTap`` transform) exports a net so the
        instantiating parent can bind it — the net keeps its name, its
        pins, and its identity; only its port flag changes.
        """
        resolved = self._resolve_net(name)
        if resolved.is_port:
            msg = f"net {name!r} is already a port"
            raise DefinitionError(msg)
        resolved._is_port = True  # noqa: SLF001 — same module
        return resolved

    def instance(
        self,
        name: str,
        subcircuit: Callable[[Circuit], None],
        /,
        **connections: Connection,
    ) -> Instance:
        """Instantiate a subcircuit: capture it, then bind its interface.

        ``subcircuit`` is a capture — a ``Subcircuit`` or any callable
        taking the fresh child circuit — run under ``name``. Every port
        the capture declares must be bound by keyword to a parent net
        (``board.instance("WD1", Watchdog(), ka=ka_net, …)``); unknown
        or unconnected ports raise, so an interface drift breaks the
        capture that introduced it, not a later stage. A port array
        binds to a sequence of equal width, element-wise; a bundle
        binds to a same-membered ``Bundle`` or mapping, member-wise.
        A port reached through two groups (the §3 power nets, aliased
        into both segment-face bundles) must resolve to one parent net
        — conflicting bindings raise.

        Component sockets bind by reference: a ``UnitHandle`` of a
        parent-placed multi-unit package packs the socket into that
        unit (``D1=u1.unit(3)``), a typed part class directs the
        standalone part (``D1=Bat54s``), and an unbound socket
        materializes as its protocol's default part at flattening.
        Packing is the parent's directed choice; one package unit
        satisfies one socket.

        The instance is capture-time structure only — nothing is
        copied into this circuit until ``flatten`` runs.
        """
        if not name:
            msg = "instance name must not be empty"
            raise DefinitionError(msg)
        _reject_separator("instance name", name)
        if name in self._instances:
            msg = f"duplicate instance name {name!r}"
            raise DefinitionError(msg)
        child = Circuit(name, self._symbols)
        subcircuit(child)
        net_connections, socket_values = self._partition_connections(name, connections)
        expanded = _expand_connections(name, child, net_connections)
        ports = child.ports
        bound_as_net = sorted(set(expanded) & set(child._sockets), key=natural_key)
        if bound_as_net:
            msg = (
                f"instance {name!r}: sockets {bound_as_net} need a unit "
                "handle or a typed part class, not a net"
            )
            raise DefinitionError(msg)
        unknown = sorted(set(expanded) - set(ports), key=natural_key)
        if unknown:
            msg = (
                f"instance {name!r}: the subcircuit has no ports {unknown} "
                f"(declared: {sorted(ports, key=natural_key)})"
            )
            raise DefinitionError(msg)
        socket_bindings, allocations = self._bind_sockets(name, child, socket_values)
        missing = sorted(set(ports) - set(expanded), key=natural_key)
        if missing:
            msg = f"instance {name!r}: ports {missing} left unconnected"
            raise DefinitionError(msg)
        resolved: dict[str, Net] = {}
        sources: dict[str, str] = {}
        for port_name, bindings in expanded.items():
            for net, source in bindings:
                target = self._resolve_net(net)
                if port_name in resolved and resolved[port_name] is not target:
                    msg = (
                        f"instance {name!r}: port {port_name!r} bound by both "
                        f"{sources[port_name]!r} and {source!r} to different nets"
                    )
                    raise DefinitionError(msg)
                resolved[port_name] = target
                sources[port_name] = source
        placed = Instance(name, child, resolved, socket_bindings, subcircuit=subcircuit)
        self._instances[name] = placed
        self._allocations.update(allocations)
        return placed

    def _partition_connections(
        self,
        name: str,
        connections: dict[str, Connection],
    ) -> tuple[dict[str, NetBinding], dict[str, UnitHandle | type[TypedPart]]]:
        """Split instance bindings into net connections and socket bindings."""
        # Lazy import: parts.py imports this module at runtime.
        from oparroy.dsl.parts import TypedPart as _TypedPart  # noqa: PLC0415

        nets: dict[str, NetBinding] = {}
        sockets: dict[str, UnitHandle | type[TypedPart]] = {}
        for key, value in connections.items():
            if isinstance(value, UnitHandle) or (
                isinstance(value, type) and issubclass(value, _TypedPart)
            ):
                sockets[key] = value
            elif isinstance(value, _TypedPart):
                msg = (
                    f"instance {name!r}: bind a part *class* ({key}=Diode), "
                    "not a constructed part — the subcircuit owns the wiring"
                )
                raise DefinitionError(msg)
            else:
                nets[key] = value
        return nets, sockets

    def _bind_sockets(
        self,
        name: str,
        child: Circuit,
        values: dict[str, UnitHandle | type[TypedPart]],
    ) -> tuple[dict[str, PackedSocket | StandaloneSocket], dict[tuple[str, int], str]]:
        """Validate socket bindings against the child's declared sockets."""
        sockets = child._sockets
        for key in values:
            if key in sockets:
                continue
            if key in child.ports or key in child._arrays or key in child._bundles:
                msg = (
                    f"instance {name!r}: {key!r} is a net port, not a "
                    "component socket; bind a net"
                )
                raise DefinitionError(msg)
            msg = (
                f"instance {name!r}: the subcircuit has no socket {key!r} "
                f"(declared: {sorted(sockets, key=natural_key)})"
            )
            raise DefinitionError(msg)
        bindings: dict[str, PackedSocket | StandaloneSocket] = {}
        allocations: dict[tuple[str, int], str] = {}
        for key, value in values.items():
            spec = sockets[key]
            if isinstance(value, UnitHandle):
                binding = self._bind_unit(name, key, spec, value, allocations)
                allocations[(binding.part.ref, binding.unit)] = f"{name}/{key}"
                bindings[key] = binding
            else:
                bindings[key] = _bind_part_class(name, key, spec, value)
        return bindings, allocations

    def _bind_unit(
        self,
        name: str,
        ref: str,
        spec: type[SocketSpec],
        handle: UnitHandle,
        allocations: dict[tuple[str, int], str],
    ) -> PackedSocket:
        """Validate packing a socket into one unit of a parent-placed part."""
        part = handle.part
        if part.symbol.is_socket:
            msg = (
                f"instance {name!r}: socket {ref!r} cannot be packed into "
                "another socket's placeholder"
            )
            raise DefinitionError(msg)
        if part is not self._parts.get(part.ref):
            msg = (
                f"instance {name!r}: {part.ref} does not belong to circuit "
                f"{self._name!r} — pack into a unit of a parent-placed part"
            )
            raise DefinitionError(msg)
        missing = sorted(set(spec.pins) - set(handle), key=natural_key)
        extra = sorted(set(handle) - set(spec.pins), key=natural_key)
        if missing or extra:
            problems = []
            if missing:
                problems.append(f"missing {missing}")
            if extra:
                problems.append(f"extra {extra}")
            msg = (
                f"instance {name!r}: {part.ref} unit {handle.unit} does not "
                f"satisfy socket {ref!r}: {' and '.join(problems)} "
                f"(protocol: {sorted(spec.pins, key=natural_key)})"
            )
            raise DefinitionError(msg)
        allocation = (part.ref, handle.unit)
        if allocation in self._allocations or allocation in allocations:
            packed_into = self._allocations.get(allocation) or allocations[allocation]
            msg = (
                f"instance {name!r}: unit {handle.unit} of {part.ref} is "
                f"already packed into {packed_into}"
            )
            raise DefinitionError(msg)
        return PackedSocket(part=part, unit=handle.unit, pin_map=handle.pin_map)

    def flatten(self) -> Circuit:
        """Reduce the instance hierarchy to a new flat circuit.

        Flattening is a pass (§7): the hierarchical capture stays the
        source, this produces the flat IR checks and emitters consume.
        Instance names prefix part references and internal nets
        (``WD1/Rs``, ``WD1/x``) — explicit names at every level keep
        identities stable across source edits — while each port net
        merges into the net its instance bound. Ports left unbound at
        the top level keep their port flag, so the dangling-net
        exemption survives the pass. The flat parts carry their
        instance path as hierarchy metadata (``Part.path``).

        Component sockets resolve here too: an unbound socket (or one
        bound to a part class) materializes as the standalone typed
        part under the instance path (``B1/D1``); a socket packed into
        a parent-placed package unit materializes no part — its pins
        are the package's physical pins, attached to the nets the
        subcircuit wired (a shared physical pin packed onto two
        different nets raises: it must sit on one).
        """
        flat = Circuit(self._name, self._symbols)
        self._flatten_into(flat, (), {}, {})
        return flat

    def _flatten_into(
        self,
        flat: Circuit,
        path: tuple[str, ...],
        bindings: dict[str, Net],
        socket_bindings: dict[str, PackedSocket | StandaloneSocket],
    ) -> None:
        prefix = "".join(f"{level}/" for level in path)
        nets: dict[Net, Net] = {}
        for name, net in self._nets.items():
            if net.is_port and name in bindings:
                nets[net] = bindings[name]
            else:
                # Prefixed names carry '/' — bypass the capture-time
                # separator check (it guards captured names only).
                created = flat._add_net(
                    f"{prefix}{name}",
                    is_port=net.is_port,
                    source=net.source,
                    sink=net.sink,
                )
                created.provenance = net.provenance
                nets[net] = created
        for part in self._parts.values():
            if part.symbol.is_socket:
                continue
            placed = flat._place(
                f"{prefix}{part.ref}",
                part.symbol,
                part.value,
                part.footprint,
                placement=part._flattened_placement(path),  # noqa: SLF001 — same module
            )
            placed.provenance = part.provenance
            placed.residuals = part.residuals
            for pin in part.pins:
                if pin.net is not None:
                    nets[pin.net]._attach(placed.pin(pin.number))  # noqa: SLF001
        self._flatten_sockets(flat, path, nets, socket_bindings)
        for inst in self._instances.values():
            child_bindings = {
                port_name: nets[net] for port_name, net in inst.connections.items()
            }
            inst.circuit._flatten_into(  # noqa: SLF001
                flat, (*path, inst.name), child_bindings, inst.socket_bindings
            )

    def _flatten_sockets(
        self,
        flat: Circuit,
        path: tuple[str, ...],
        nets: dict[Net, Net],
        socket_bindings: dict[str, PackedSocket | StandaloneSocket],
    ) -> None:
        """Resolve each socket: standalone part or packed package unit."""
        prefix = "".join(f"{level}/" for level in path)
        # Packed units belong to the parent circuit, flattened one
        # level up — the parent's parts are already placed.
        parent_prefix = "".join(f"{level}/" for level in path[:-1])
        for ref, spec in self._sockets.items():
            placeholder = self._parts[ref]
            binding = socket_bindings.get(ref)
            if isinstance(binding, PackedSocket):
                target = flat._parts[f"{parent_prefix}{binding.part.ref}"]
                for pin in placeholder.pins:
                    if pin.net is not None:
                        nets[pin.net]._attach(  # noqa: SLF001
                            target.pin(binding.pin_map[pin.number])
                        )
                continue
            part_class = spec.default if binding is None else binding.part_class
            placed = flat._place(
                f"{prefix}{ref}",
                flat._symbols.lookup(part_class.symbol),
                part_class.default_value,
                part_class.default_footprint,
                placement=Placement(path=path),
            )
            placed.provenance = placeholder.provenance
            placed.residuals = part_class.residuals
            for pin in placeholder.pins:
                if pin.net is not None:
                    for number in _pin_numbers(part_class.pin_map[pin.number]):
                        nets[pin.net]._attach(placed.pin(number))  # noqa: SLF001

    def renamed(self, refs: Mapping[str, str]) -> Circuit:
        """Apply annotation: a flat copy with parts renamed to their refdes.

        The annotation stage (``oparroy.dsl.annotate``) maps capture
        names to placed refdes; this pass materializes the renamed IR
        the netlist emitter consumes. Each part keeps its capture name
        as ``Part.identity``, so the emitted tstamps stay stable across
        re-annotation and pcbnew keeps matching parts by timestamp.
        Parts missing from ``refs`` keep their current ref (power
        symbols are never annotated). A rename that collides raises like
        any duplicate reference.
        """
        if self._instances:
            return self.flatten().renamed(refs)
        renamed = Circuit(self._name, self._symbols)
        nets: dict[Net, Net] = {}
        for name, net in self._nets.items():
            copied = renamed._add_net(name, is_port=net.is_port)
            copied.provenance = net.provenance
            nets[net] = copied
        for part in self._parts.values():
            placed = renamed._place(
                refs.get(part.identity, refs.get(part.ref, part.ref)),
                part.symbol,
                part.value,
                part.footprint,
                identity=part.identity,
                # The empty prefix keeps the part's own path as-is.
                placement=part._flattened_placement(()),  # noqa: SLF001 — same module
            )
            placed.provenance = part.provenance
            placed.residuals = part.residuals
            for pin in part.pins:
                if pin.net is not None:
                    nets[pin.net]._attach(placed.pin(pin.number))  # noqa: SLF001
        return renamed

    def dump(self) -> str:
        """Pretty-print the IR for humans; not a round-trip format."""
        header = (
            f"circuit {self._name}: {len(self._parts)} parts, {len(self._nets)} nets"
        )
        lines = [header, "parts:"]
        for ref in sorted(self._parts, key=natural_key):
            part = self._parts[ref]
            value = part.value if part.value is not None else "?"
            footprint = f" [{part.footprint}]" if part.footprint is not None else ""
            lines.append(f"  {ref} {part.symbol.ref} {value!r}{footprint}")
            for pin in part.pins:
                target = pin.net.name if pin.net is not None else "—"
                name = f" {pin.name!r}" if pin.name else ""
                lines.append(f"    {pin.number}{name} ({pin.type}) -> {target}")
        lines.append("nets:")
        for name in sorted(self._nets, key=natural_key):
            net = self._nets[name]
            members = " ".join(f"{p.part.ref}.{p.number}" for p in net.pins)
            flags = []
            if net.is_port:
                flags.append("port")
            if net.source is not None:
                flags.append(f"source {net.source}")
            if net.sink is not None:
                flags.append(f"sink {net.sink}")
            marker = f" [{', '.join(flags)}]" if flags else ""
            lines.append(f"  {name}{marker}: {members}")
        for name, array in self._arrays.items():
            lines.append(f"port array {name}[{len(array)}]")
        for name, bundle in self._bundles.items():
            members = " ".join(f"{member}={bundle[member].name}" for member in bundle)
            lines.append(f"bundle {name}: {members}")
        for name in self._instances:
            lines.append(f"instance {name}:")
            child_dump = self._instances[name].circuit.dump()
            lines.extend(f"  {line}" for line in child_dump.splitlines())
        return "\n".join(lines)

    def __str__(self) -> str:
        return self.dump()


def hierarchical_waivers(circuit: Circuit) -> list[Waiver]:
    """Gather a circuit's and its instances' waivers, paths fully prefixed.

    A waiver declared inside a subcircuit addresses a path relative to
    that subcircuit; instantiation prefixes it with the instance path,
    so ``IN1/vin`` inside ``WD1`` addresses ``WD1/IN1/vin``. The
    validation pass applies these; ``Instance.flatten_hierarchy``
    re-homes them on the per-tile flat form.
    """
    return _collect_waivers(circuit, ())


def _collect_waivers(circuit: Circuit, prefix: tuple[str, ...]) -> list[Waiver]:
    base = "/".join(prefix)
    collected = [
        Waiver(w.check, f"{base}/{w.path}" if base else w.path, w.reason)
        for w in circuit.waivers
    ]
    for instance in circuit.instances.values():
        collected.extend(_collect_waivers(instance.circuit, (*prefix, instance.name)))
    return collected
