kristofferkoch/oparroy/tests/test_dsl_pcb.py

"""`.kicad_pcb` parser tests: the pass-board fixture and edge cases."""

from __future__ import annotations

import math

import pytest

from oparroy.dsl import Board, EdgeKind, PcbError, Point, parse_board
from oparroy.dsl.sexpr import SexpError

_THICKNESS_MM = 1.6
_DEFAULT_CLEARANCE_MM = 0.2
_DEFAULT_WIDTH_MM = 0.25
_BYPASS_WIDTH_MM = 0.5
_ARC_WIDTH_MM = 0.4
_VIA_SIZE_MM = 0.8
_MOUNTING_HOLES = 4


def test_rejects_non_board_document() -> None:
    with pytest.raises(PcbError, match=r"not a .kicad_pcb document"):
        parse_board('(kicad_symbol_lib (symbol "R"))')


def test_rejects_malformed_sexpr() -> None:
    with pytest.raises(SexpError):
        parse_board("(kicad_pcb (layers")


def test_stackup(board_pass: Board) -> None:
    assert board_pass.thickness_mm == _THICKNESS_MM
    assert board_pass.copper_layers == ("F.Cu", "B.Cu")
    assert board_pass.silkscreen_layers == ("B.SilkS", "F.SilkS")


def test_net_table(board_pass: Board) -> None:
    assert board_pass.nets == {"": 0, "BYPASS": 1, "GND": 2, "SIG": 3}


def test_net_classes() -> None:
    """Board-file net classes: the pre-KiCad-10 fallback the parser keeps."""
    board = parse_board(
        "(kicad_pcb (layers)"
        " (setup"
        '  (net_class "Default" "" (clearance 0.2) (trace_width 0.25)'
        '   (add_net "GND") (add_net "SIG"))'
        '  (net_class "Power" "" (trace_width 0.5) (add_net "BYPASS")))'
        ' (net 1 "BYPASS") (net 2 "GND") (net 3 "SIG"))'
    )
    by_name = {nc.name: nc for nc in board.net_classes}
    assert set(by_name) == {"Default", "Power"}
    default = by_name["Default"]
    assert default.trace_width_mm == _DEFAULT_WIDTH_MM
    assert default.clearance_mm == _DEFAULT_CLEARANCE_MM
    assert default.nets == frozenset({"GND", "SIG"})
    assert by_name["Power"].nets == frozenset({"BYPASS"})
    power = board.net_class_of("BYPASS")
    assert power is not None
    assert power.name == "Power"
    assert board.net_class_of("UNROUTE") is None


def test_footprints_and_pads(board_pass: Board) -> None:
    by_ref = {fp.ref: fp for fp in board_pass.footprints}
    assert set(by_ref) == {"J1", "J2", "SW1", "D1", "D2", "H1", "H2", "H3", "H4"}
    assert by_ref["J1"].at == Point(60, 60)
    assert by_ref["J1"].lib == "Connector:CONN_1x06"
    assert [(pad.number, pad.net) for pad in by_ref["SW1"].pads] == [
        ("1", "BYPASS"),
        ("2", "BYPASS"),
        ("3", "SIG"),
    ]
    assert by_ref["H1"].pads[0].kind == "np_thru_hole"


def test_legacy_fp_text_reference() -> None:
    board = parse_board(
        '(kicad_pcb (layers) (footprint "Lib:Name" (layer "F.Cu") (at 1 2 0)'
        ' (fp_text reference "R7" (at 0 0 0) (layer "F.SilkS"))))'
    )
    assert board.footprints[0].ref == "R7"
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
